GPro97/Projet_gestion_camion/images/img1.jpg

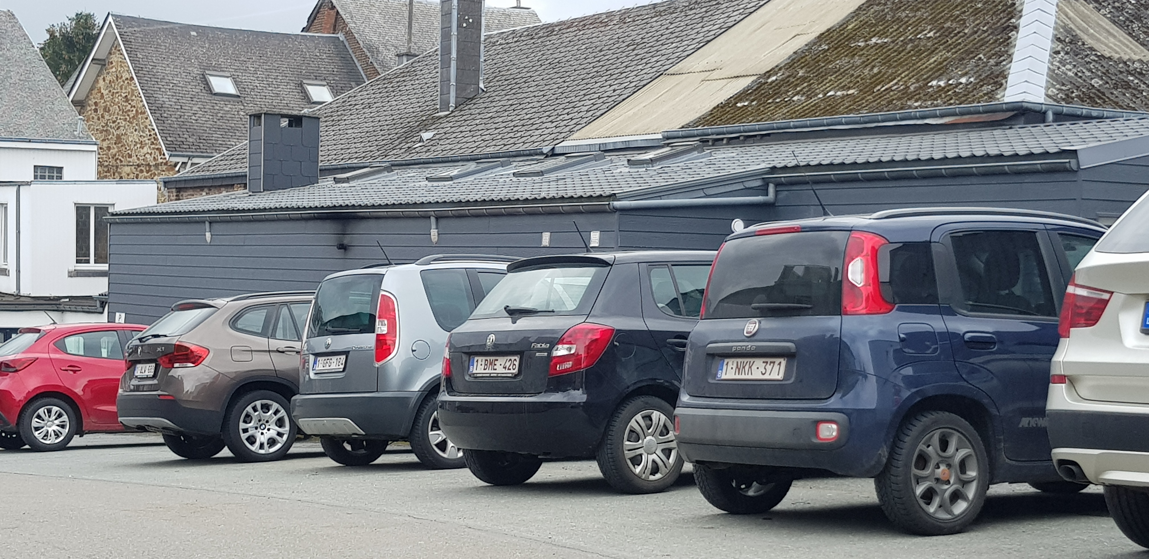
images/img1.jpg
