GPro97/Projet_gestion_camion/images/img3.jpg

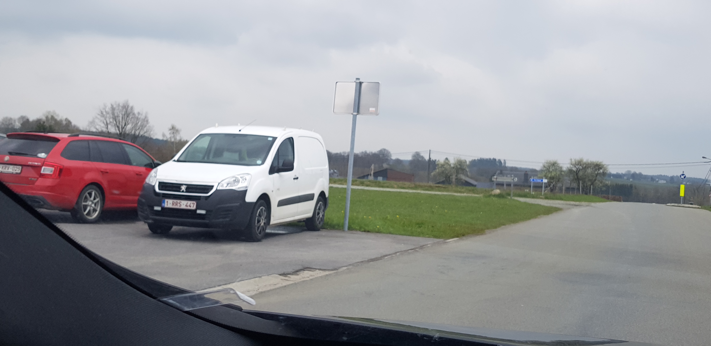
images/img3.jpg
