GPro97/Projet_gestion_camion/images/img4.jpg

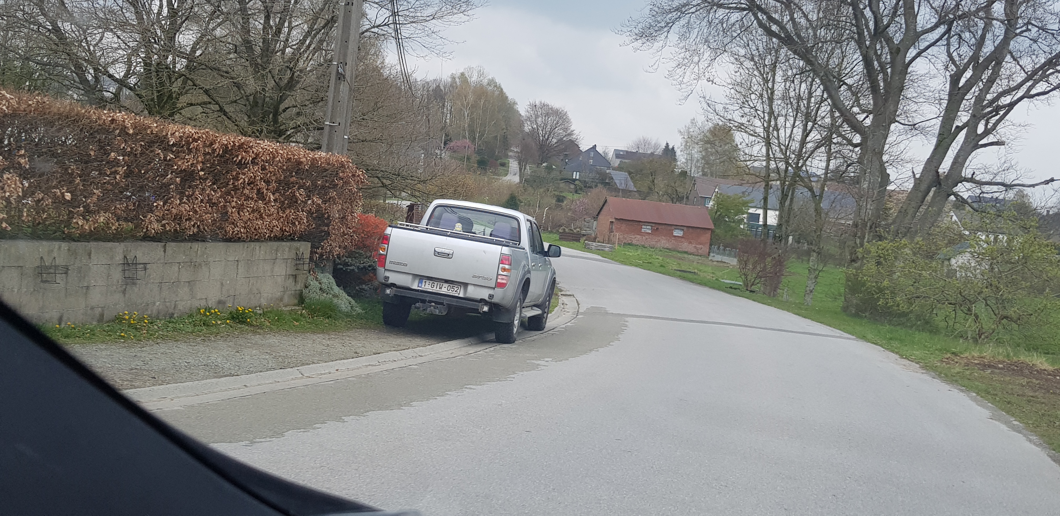
images/img4.jpg
