GPro97/Projet_gestion_camion/images/img5.jpg

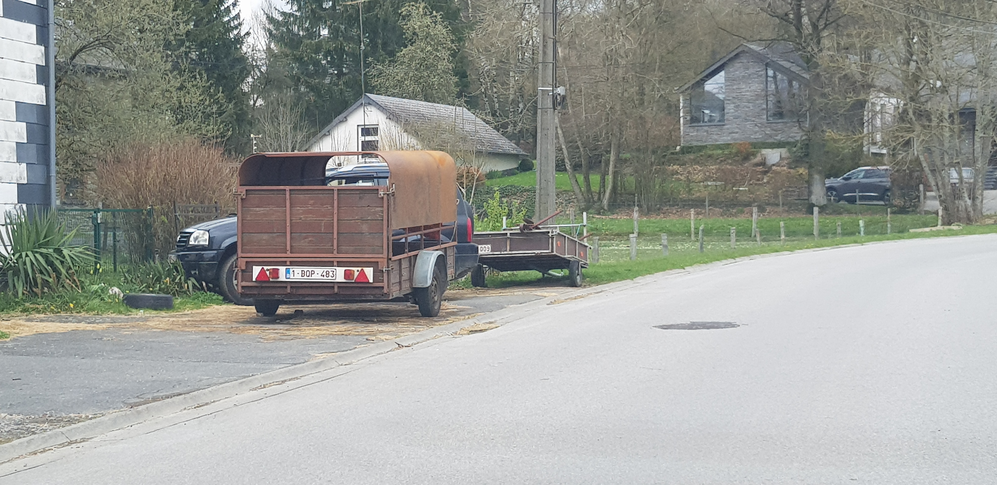
images/img5.jpg
