GPro97/Projet_gestion_camion/images/img8.jpg

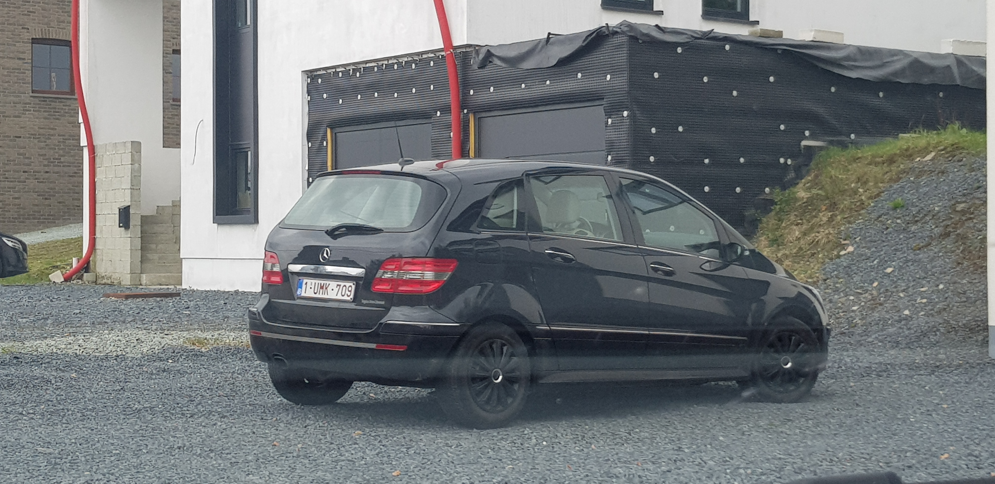
images/img8.jpg
