GPro97/Projet_gestion_camion/images/img9.jpg

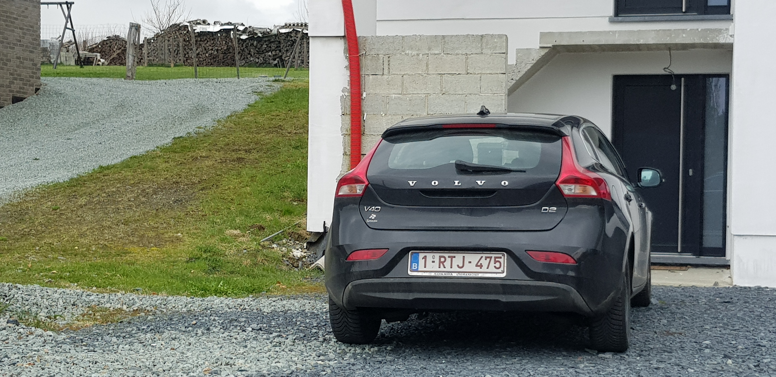
images/img9.jpg
