GPro97/Projet_gestion_camion/images/img10.jpg

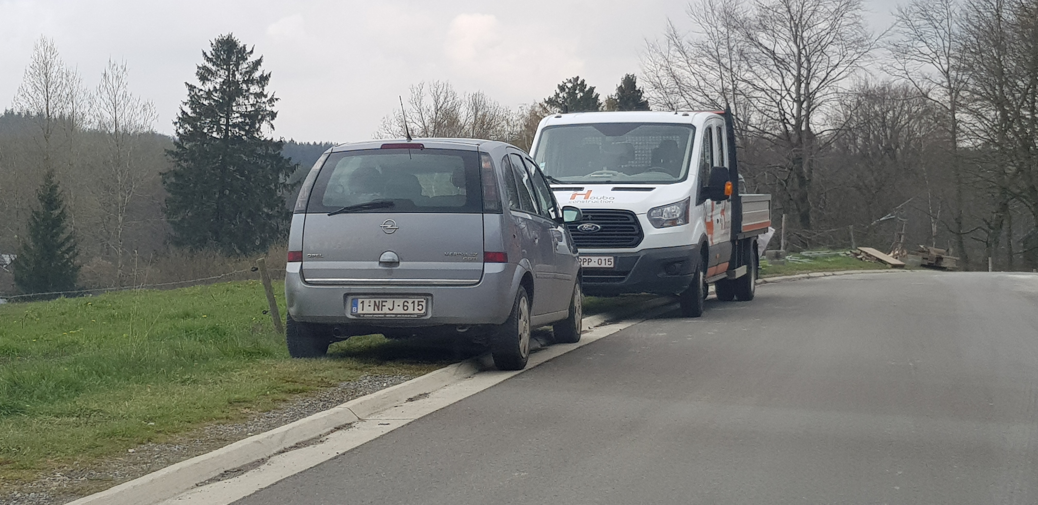
images/img10.jpg
