GPro97/Projet_gestion_camion/images/img11.jpg

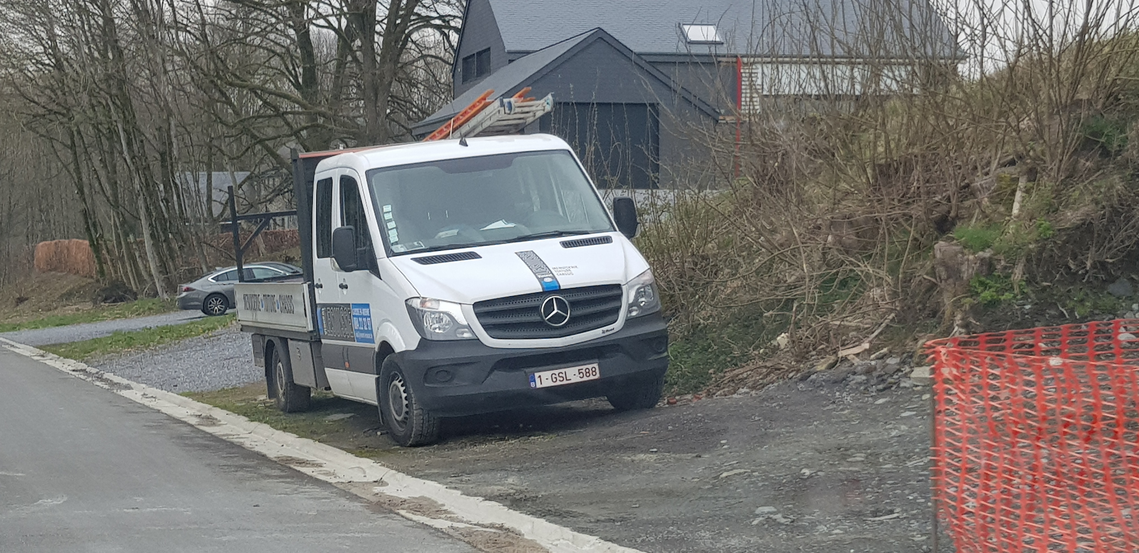
images/img11.jpg
