GPro97/Projet_gestion_camion/images/img12.jpg

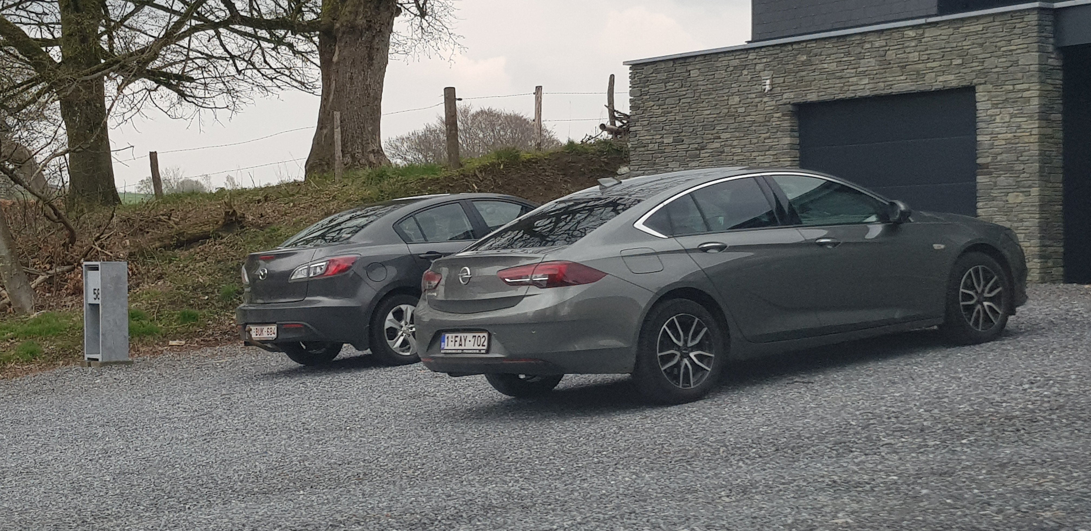
images/img12.jpg
