GPro97/Projet_gestion_camion/images/img13.jpg

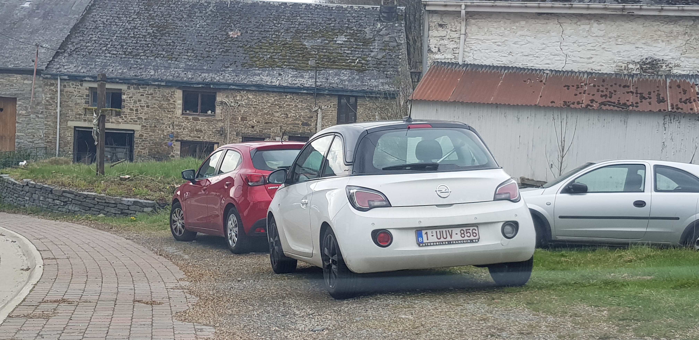
images/img13.jpg
