GPro97/Projet_gestion_camion/images/img14.jpg

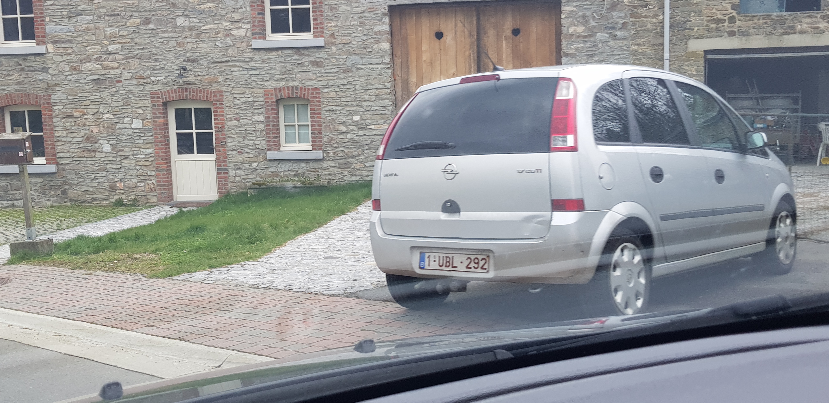
images/img14.jpg
