GPro97/Projet_gestion_camion/images/img15.jpg

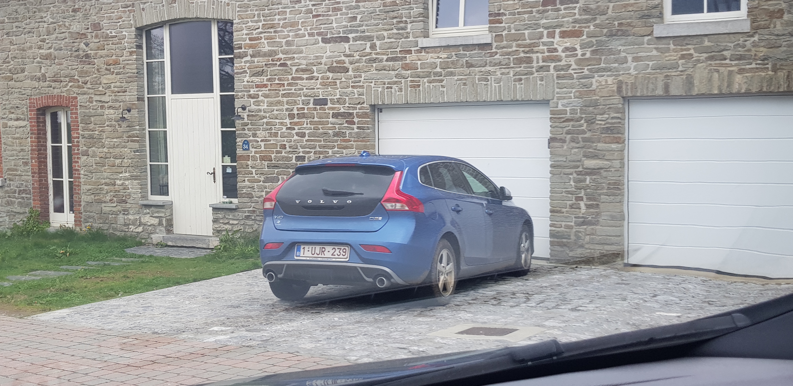
images/img15.jpg
