GPro97/Projet_gestion_camion/images/img16.jpg

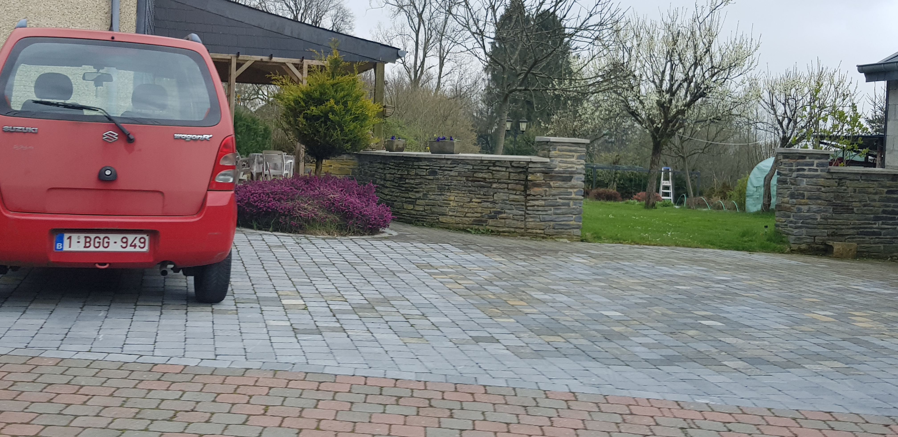
images/img16.jpg
