GPro97/Projet_gestion_camion/images/img17.jpg

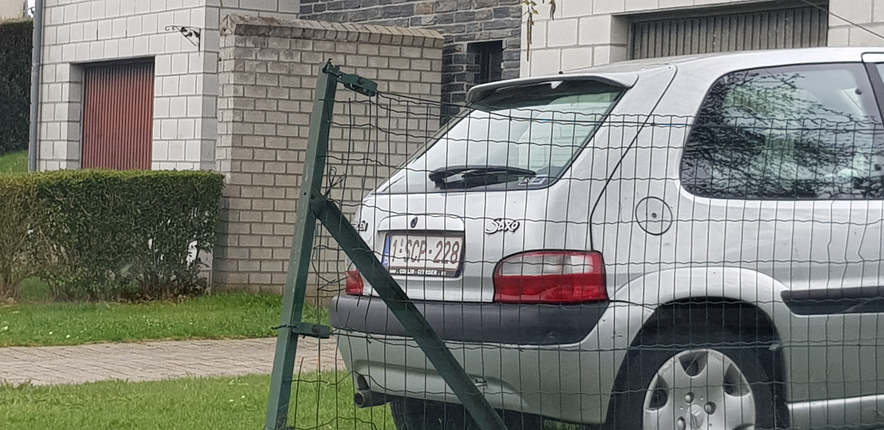
images/img17.jpg
