GPro97/Projet_gestion_camion/images/img18.jpg

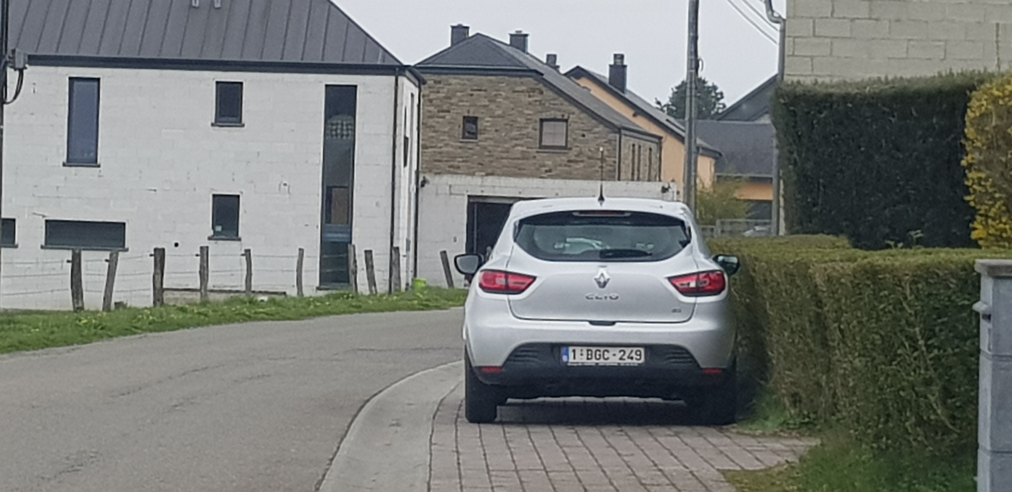
images/img18.jpg
