GPro97/Projet_gestion_camion/images/img19.jpg

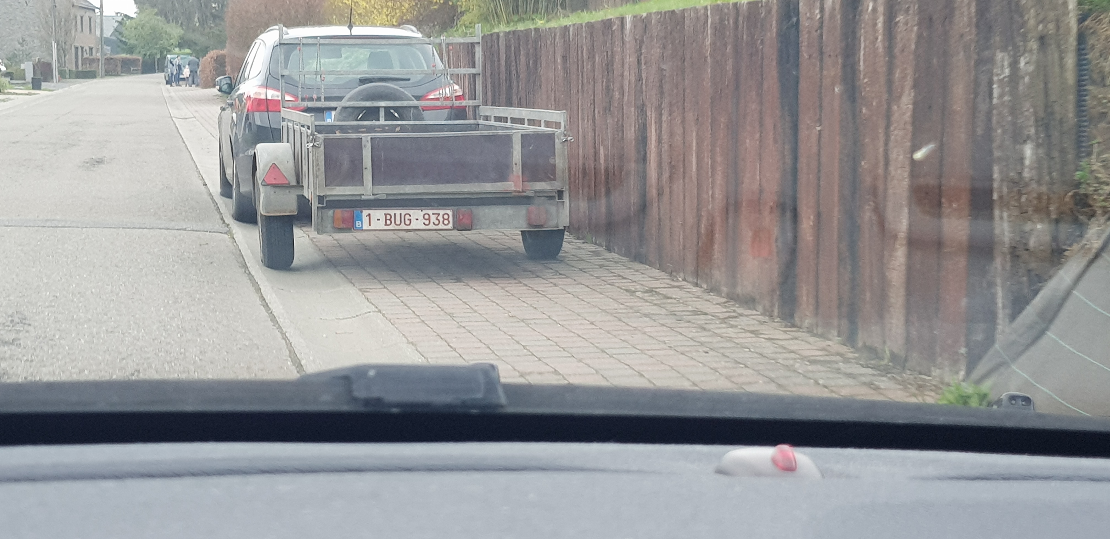
images/img19.jpg
