GPro97/Projet_gestion_camion/images/img21.jpg

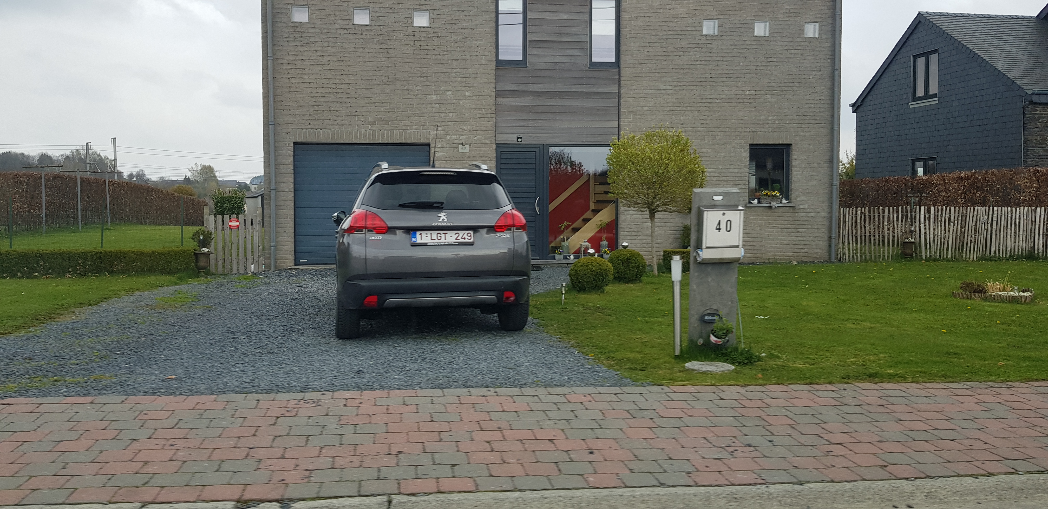
images/img21.jpg
