GPro97/Projet_gestion_camion/images/img23.jpg

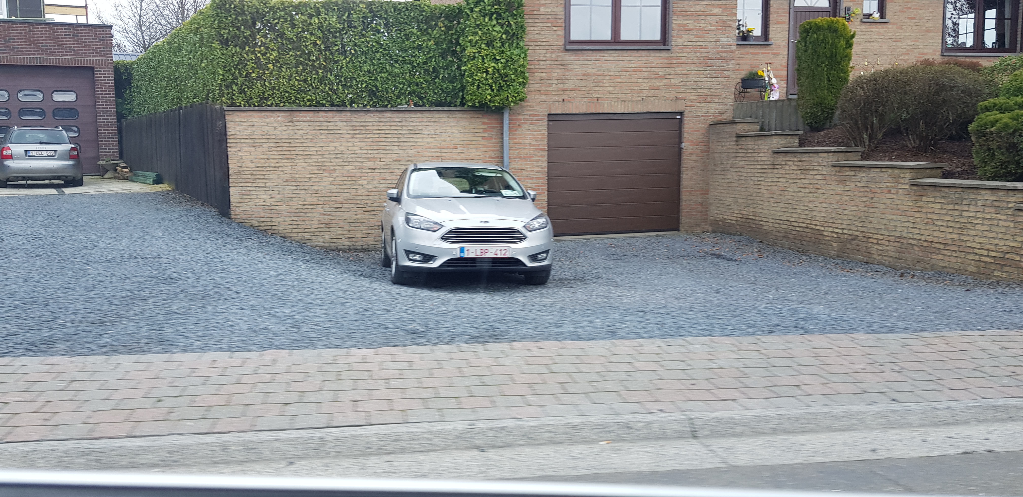
images/img23.jpg
