GPro97/Projet_gestion_camion/images/img24.jpg

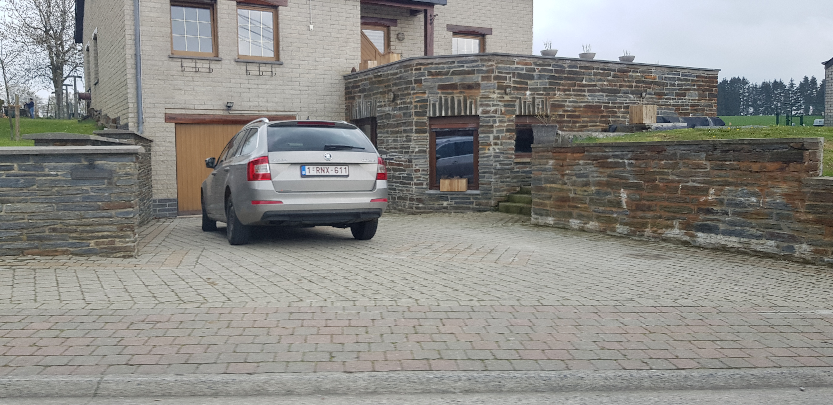
images/img24.jpg
