GPro97/Projet_gestion_camion/images/img25.jpg

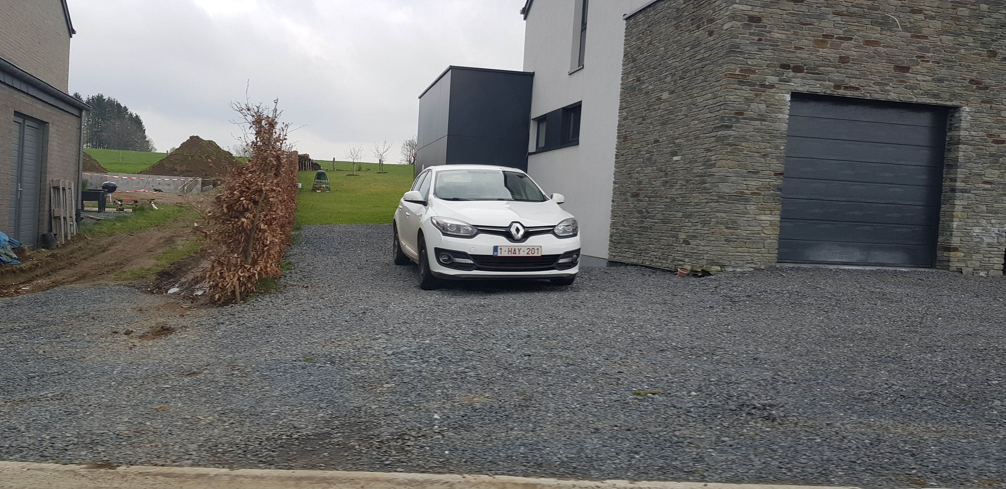
images/img25.jpg
