GPro97/Projet_gestion_camion/images/img26.jpg

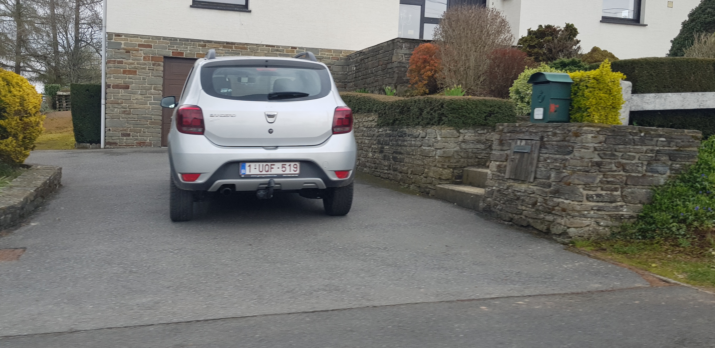
images/img26.jpg
