GPro97/Projet_gestion_camion/images/img27.jpg

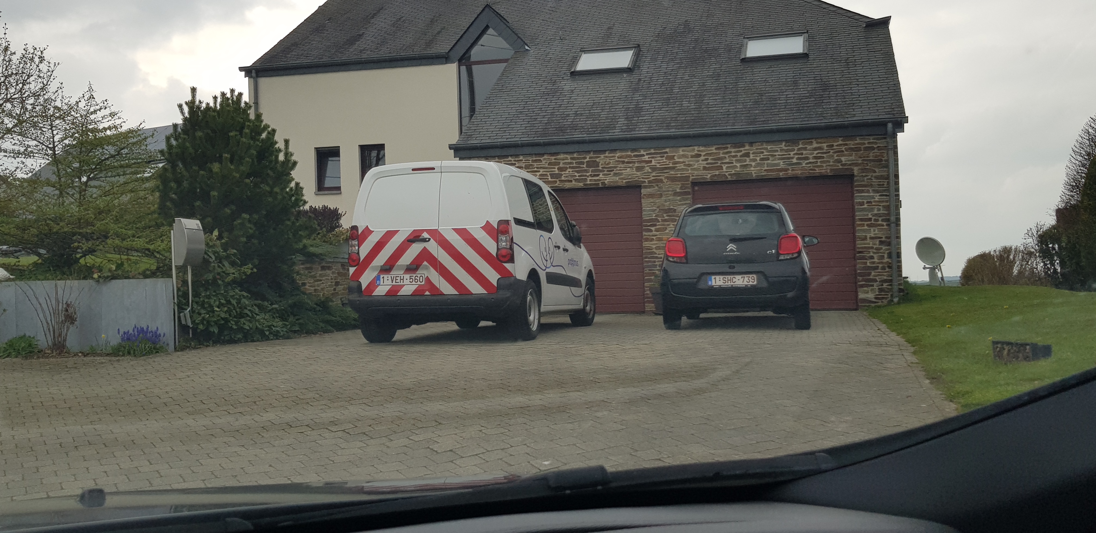
images/img27.jpg
