GPro97/Projet_gestion_camion/images/img28.jpg

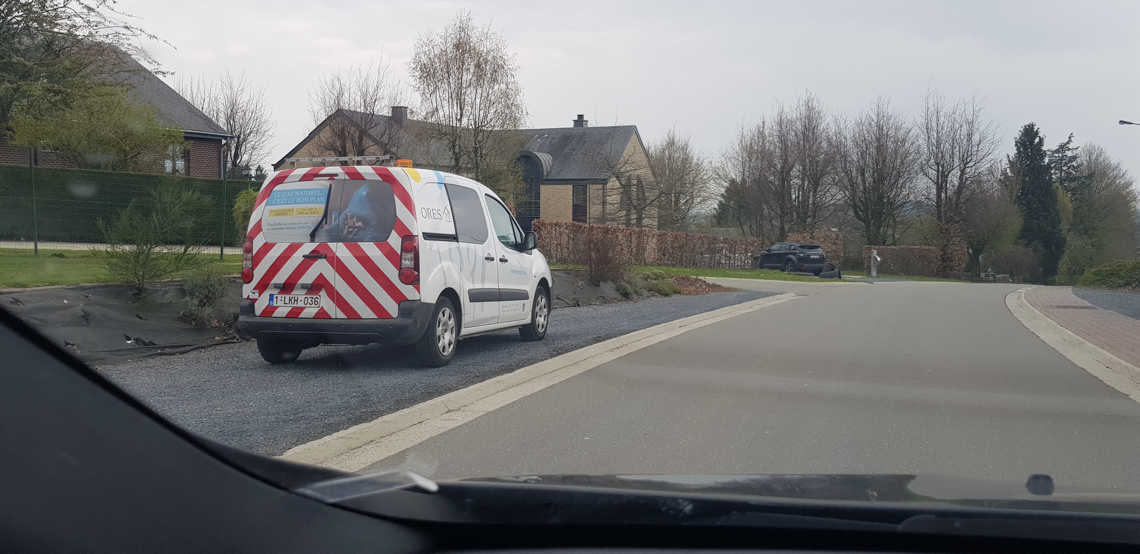
images/img28.jpg
