GPro97/Projet_gestion_camion/images/img29.jpg

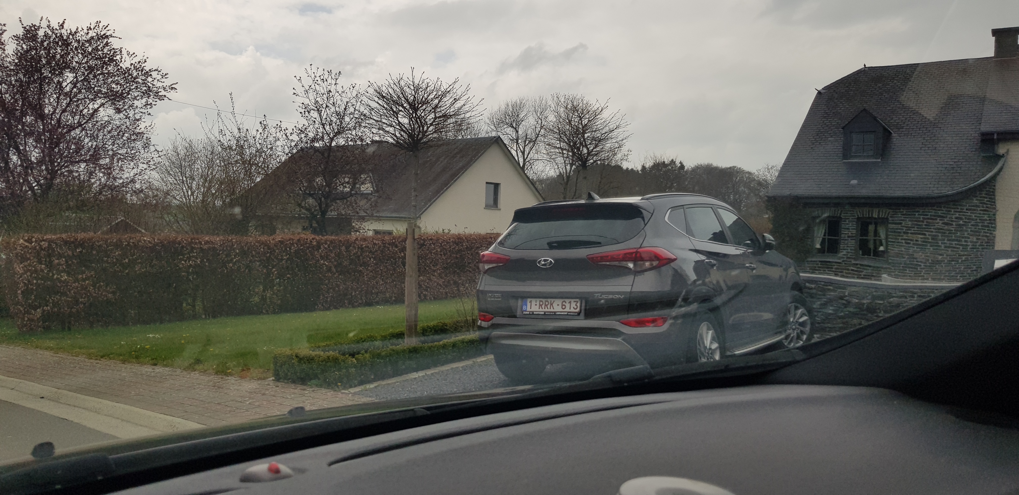
images/img29.jpg
