GPro97/Projet_gestion_camion/images/img31.jpg

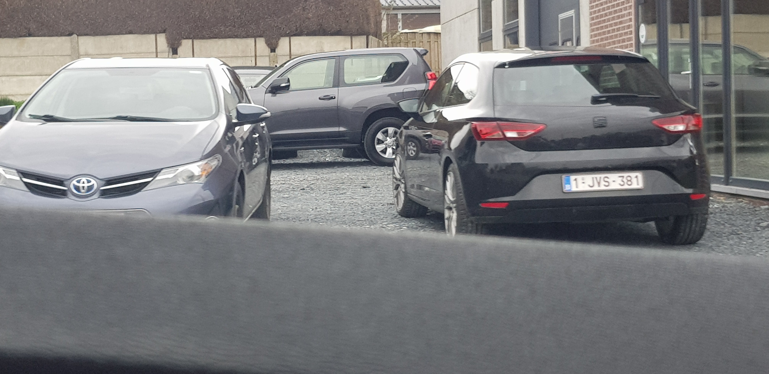
images/img31.jpg
