GPro97/Projet_gestion_camion/images/img32.jpg

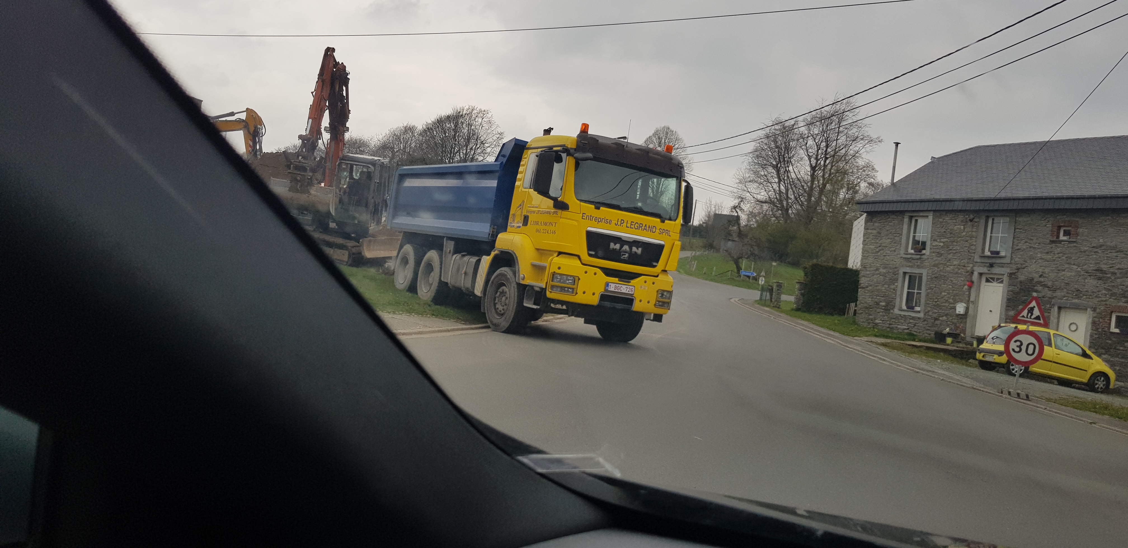
images/img32.jpg
