GPro97/Projet_gestion_camion/images/img33.jpg

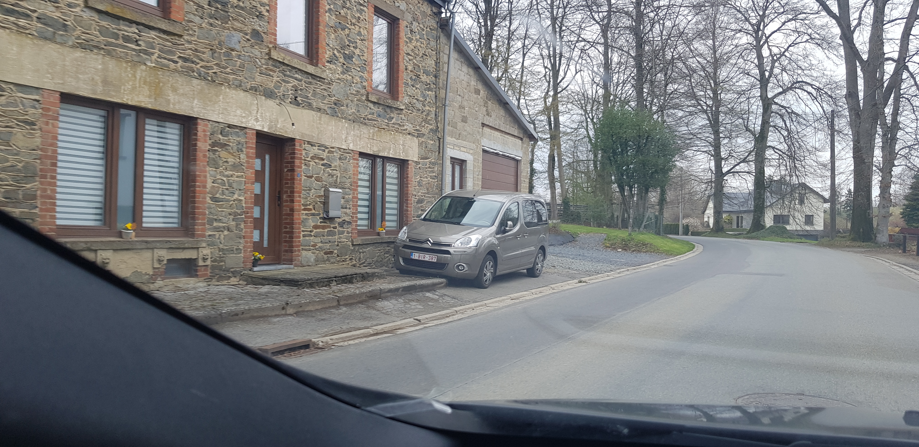
images/img33.jpg
