GPro97/Projet_gestion_camion/images/img34.jpg

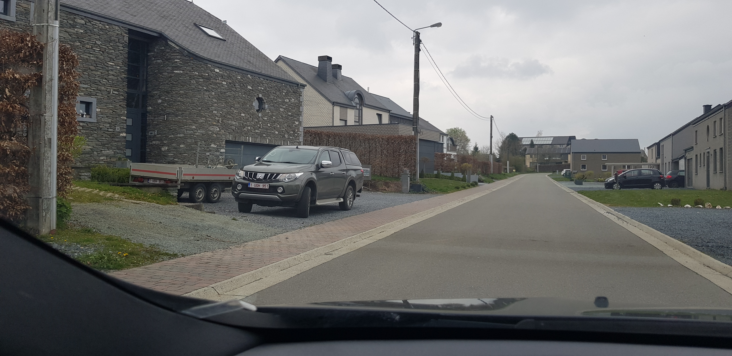
images/img34.jpg
