GPro97/Projet_gestion_camion/images/img36.jpg

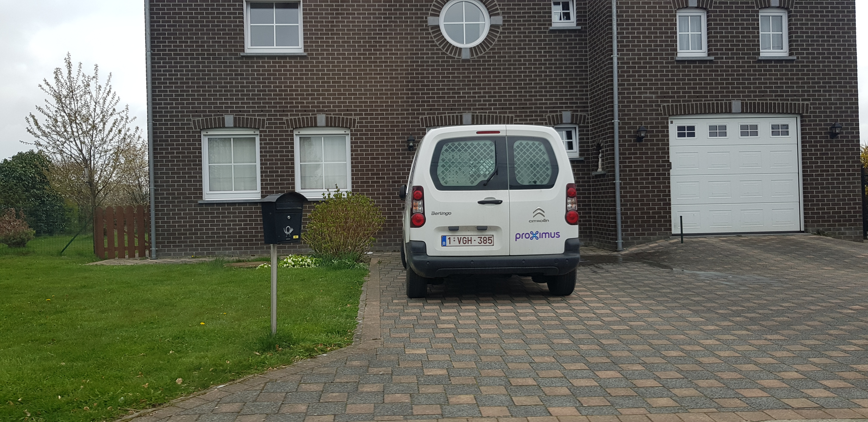
images/img36.jpg
