GPro97/Projet_gestion_camion/images/img37.jpg

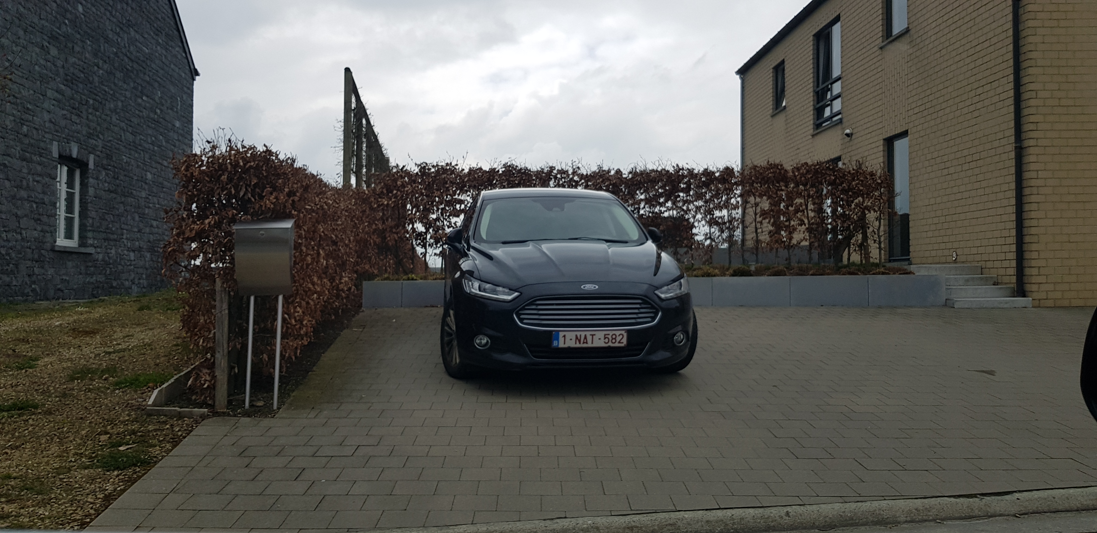
images/img37.jpg
