GPro97/Projet_gestion_camion/images/img38.jpg

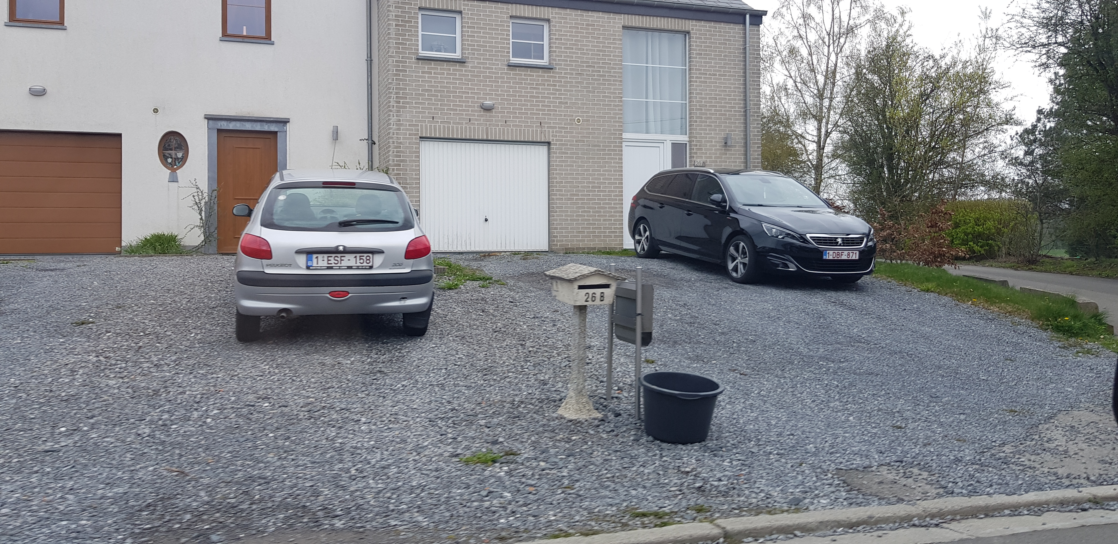
images/img38.jpg
