GPro97/Projet_gestion_camion/images/img39.jpg

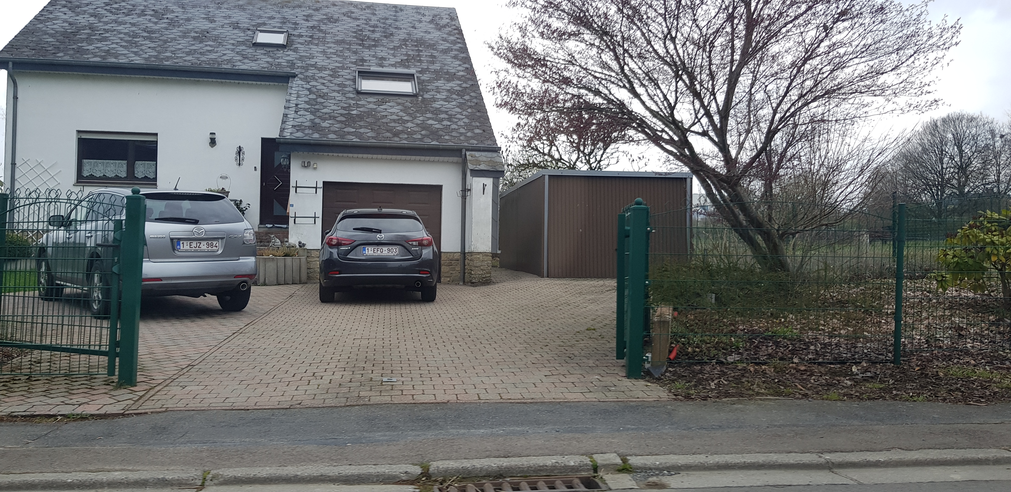
images/img39.jpg
