GPro97/Projet_gestion_camion/images/img40.jpg

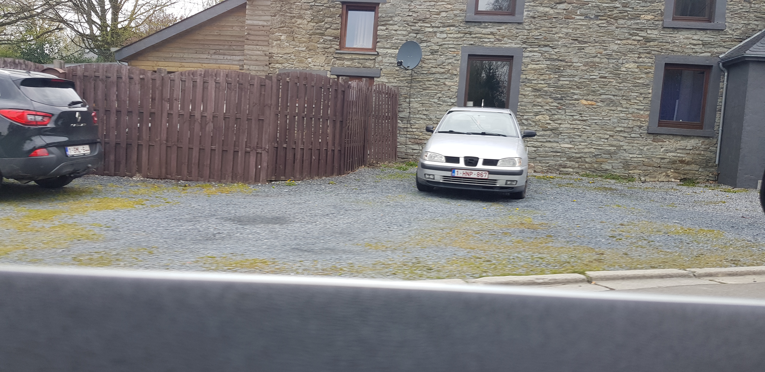
images/img40.jpg
