GPro97/Projet_gestion_camion/images/img41.jpg

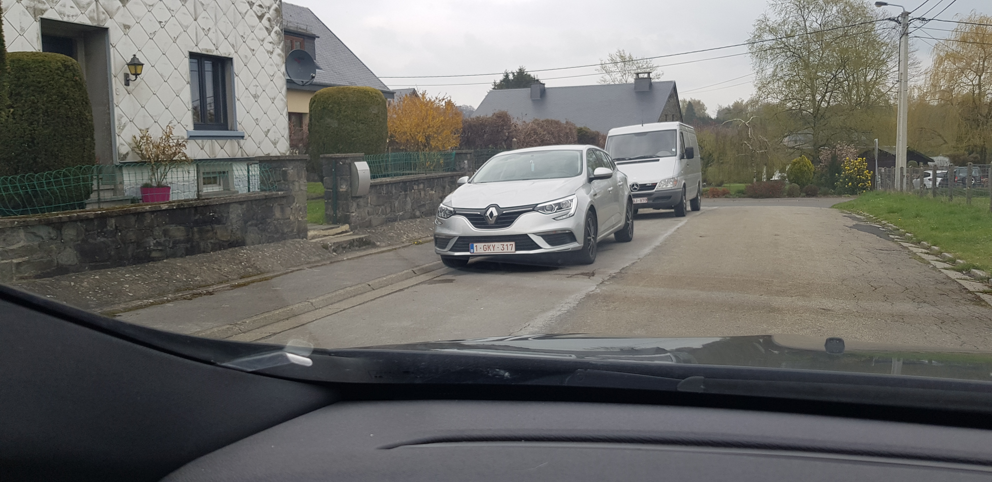
images/img41.jpg
