GPro97/Projet_gestion_camion/images/img42.jpg

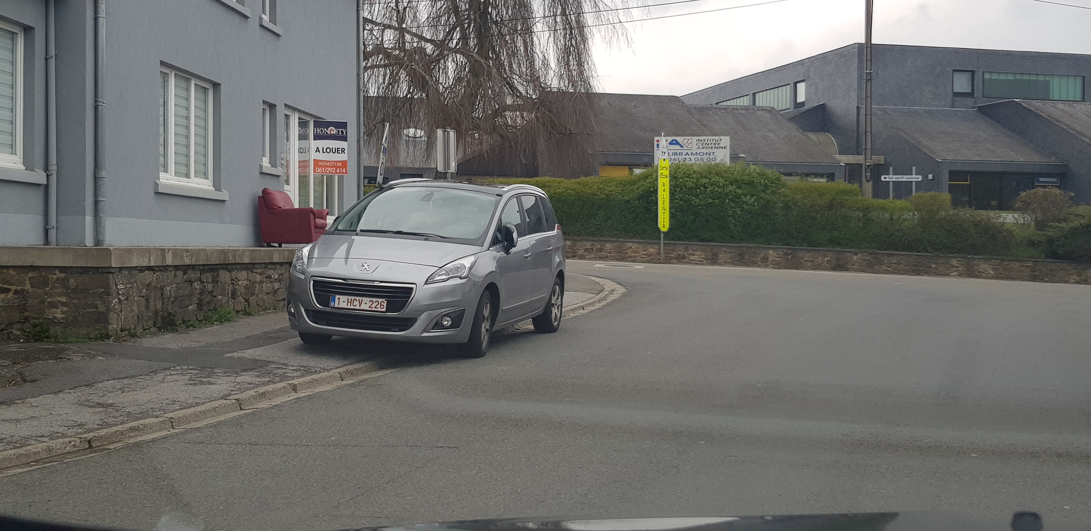
images/img42.jpg
