GPro97/Projet_gestion_camion/images/img43.jpg

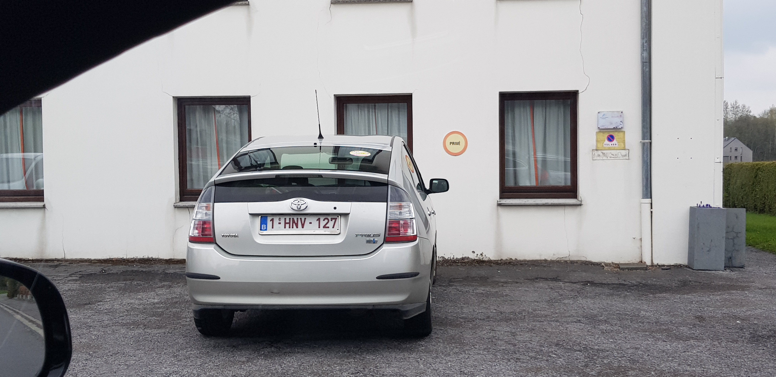
images/img43.jpg
