GPro97/Projet_gestion_camion/images/img44.jpg

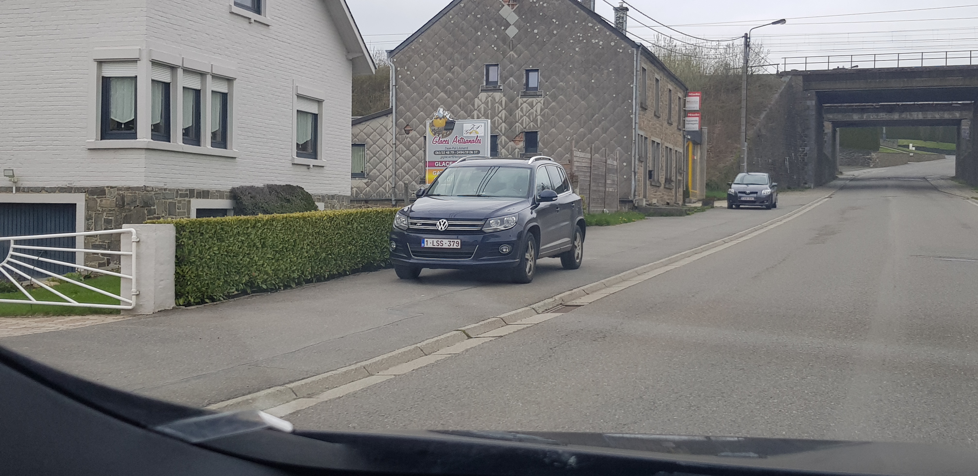
images/img44.jpg
