GPro97/Projet_gestion_camion/images/img45.jpg

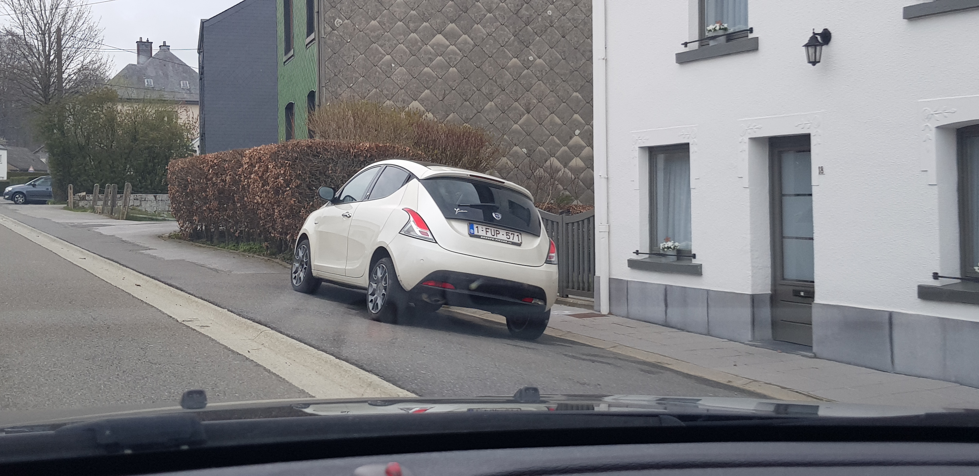
images/img45.jpg
