GPro97/Projet_gestion_camion/images/img46.jpg

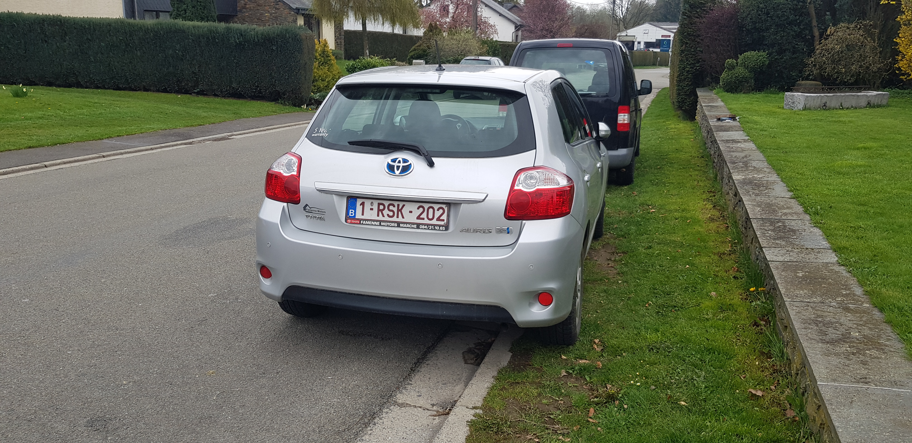
images/img46.jpg
