GPro97/Projet_gestion_camion/images/img47.jpg

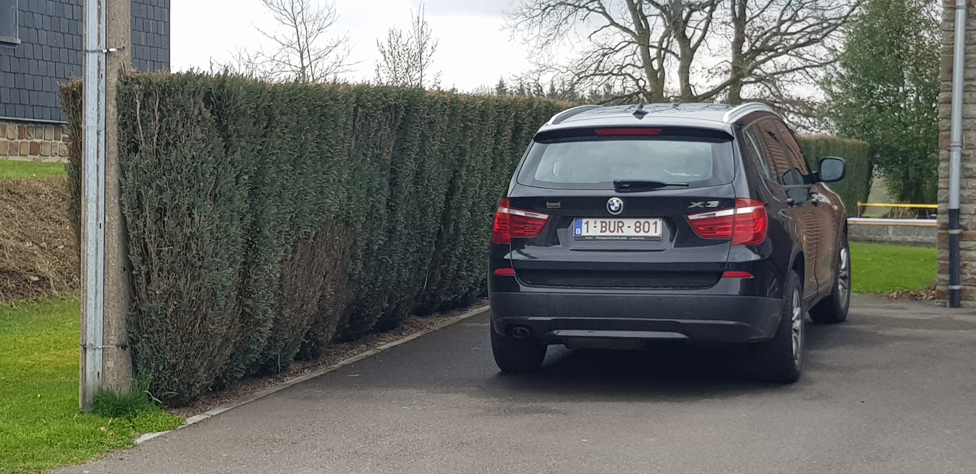
images/img47.jpg
