GPro97/Projet_gestion_camion/images/img48.jpg

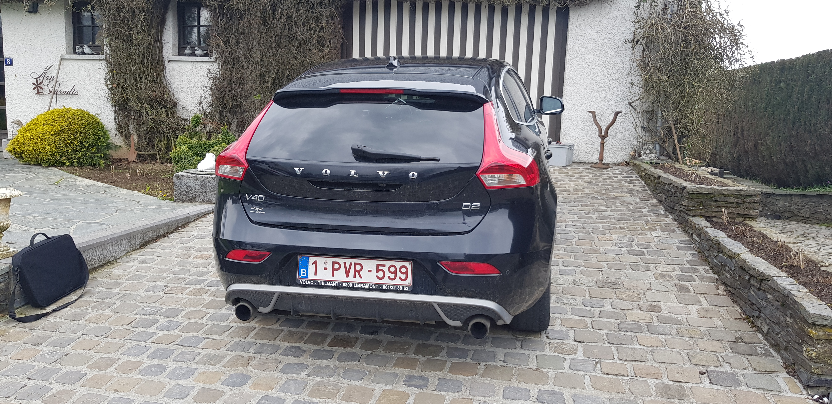
images/img48.jpg
