GPro97/Projet_gestion_camion/images/img49.jpg

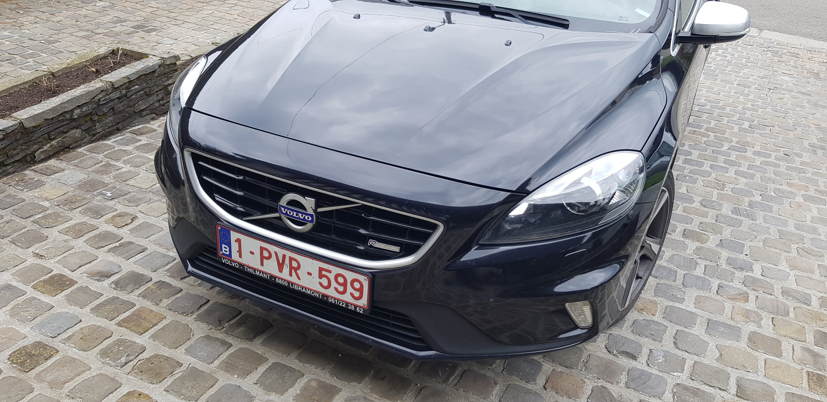
images/img49.jpg
