GPro97/Projet_gestion_camion/images/img50.jpg

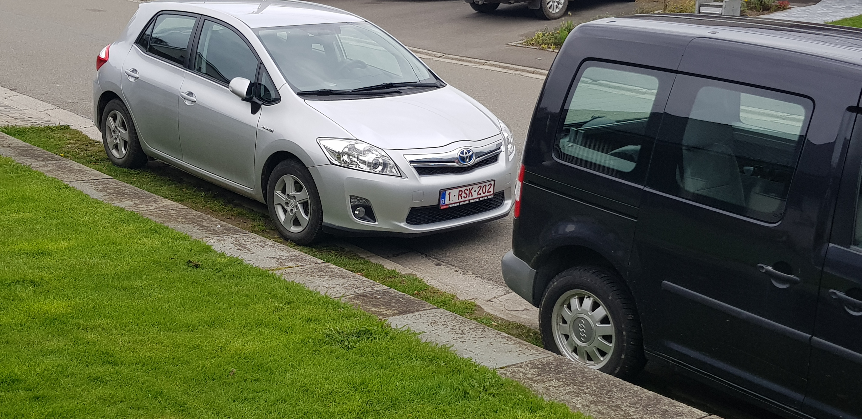
images/img50.jpg
