GPro97/Projet_gestion_camion/images/img51.jpg

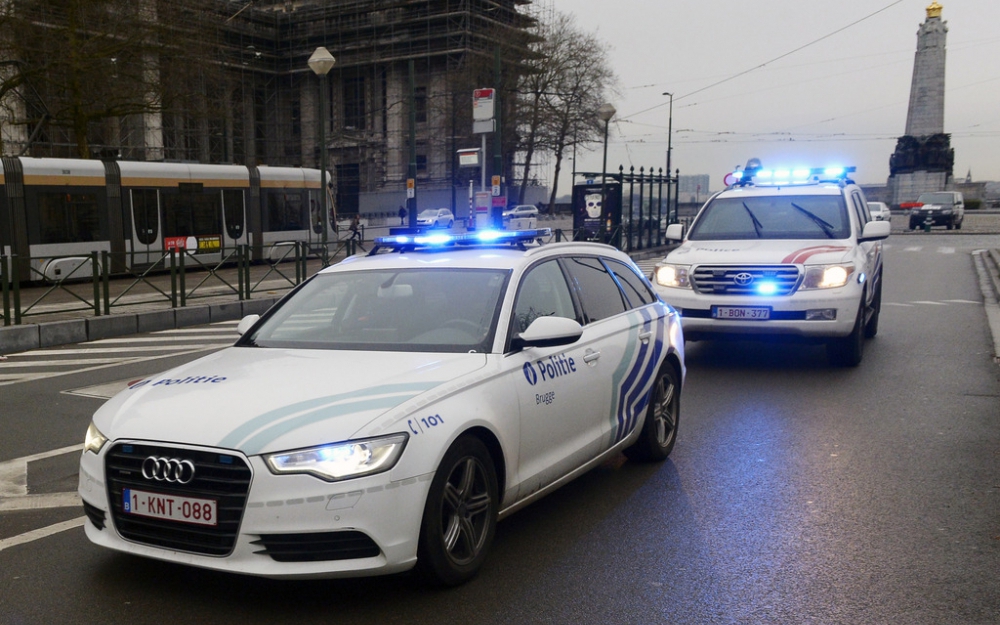
images/img51.jpg
