GPro97/Projet_gestion_camion/images/img52.jpg

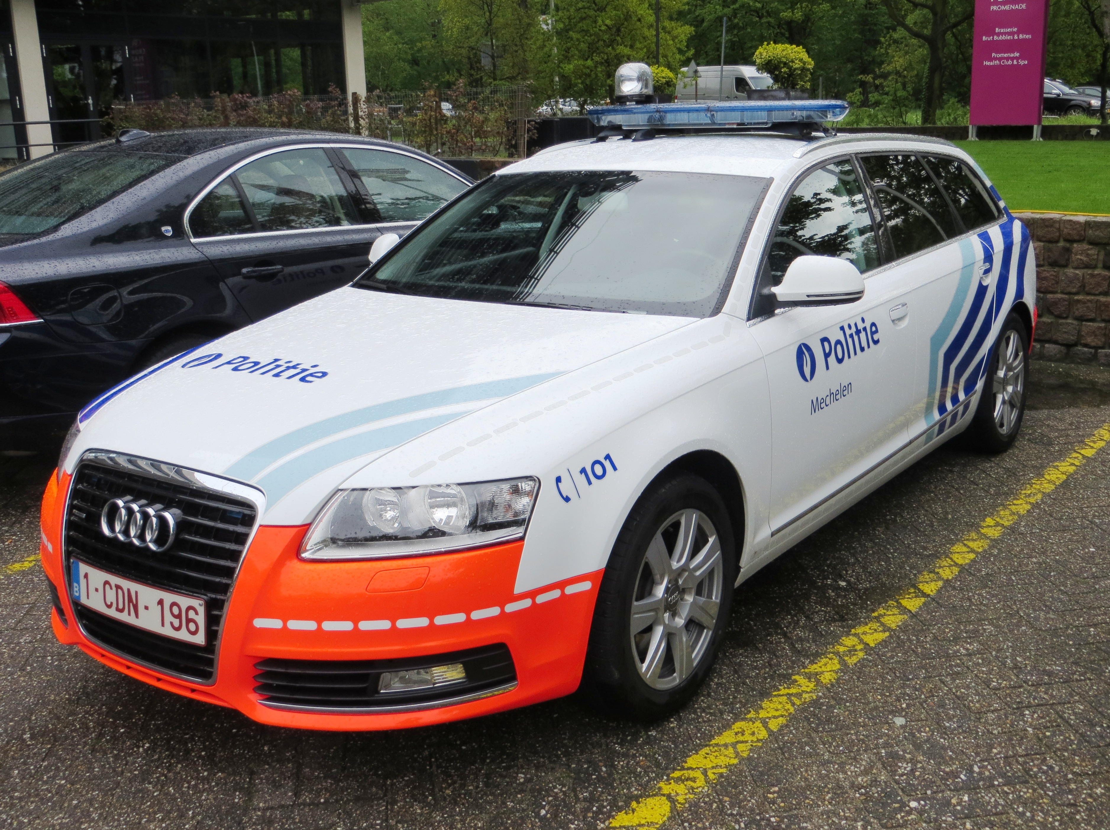
images/img52.jpg
