GPro97/Projet_gestion_camion/images/img53.jpg

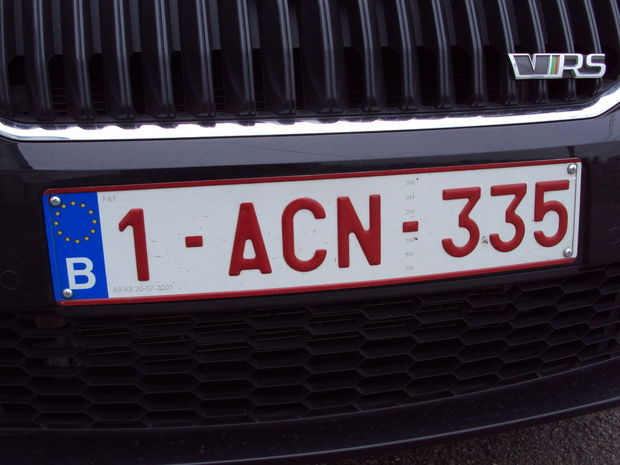
images/img53.jpg
