GPro97/Projet_gestion_camion/images/img54.jpg

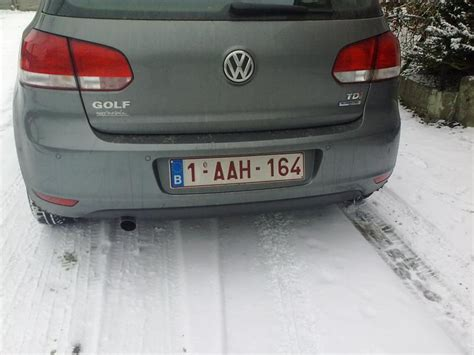
images/img54.jpg
