GPro97/Projet_gestion_camion/images/img56.jpg

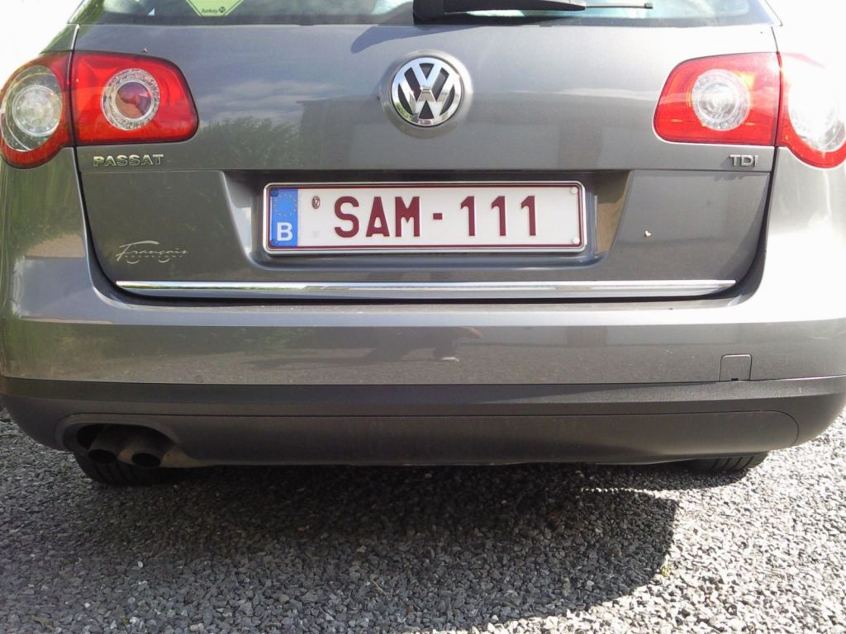
images/img56.jpg
