GPro97/Projet_gestion_camion/images/img59.jpg

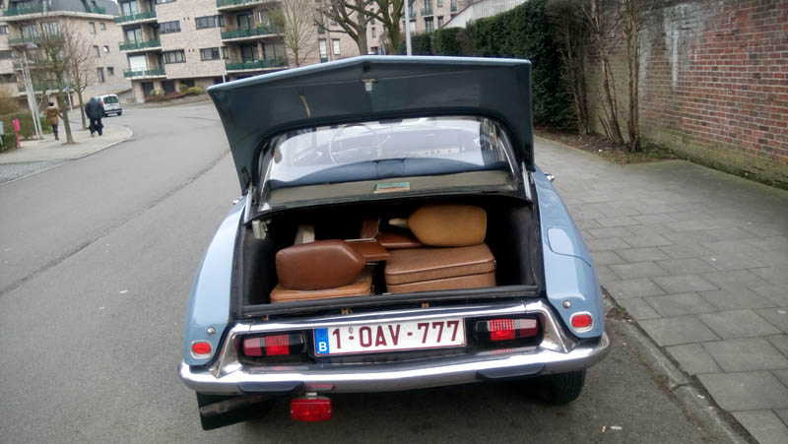
images/img59.jpg
