GPro97/Projet_gestion_camion/images/img60.jpg

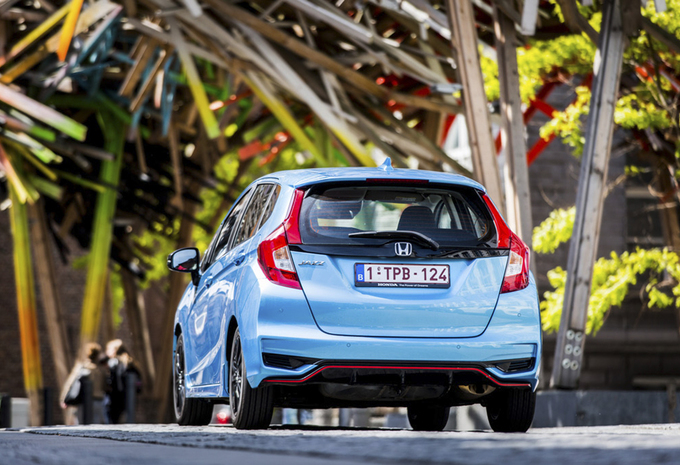
images/img60.jpg
