GPro97/Projet_gestion_camion/images/img61.jpg

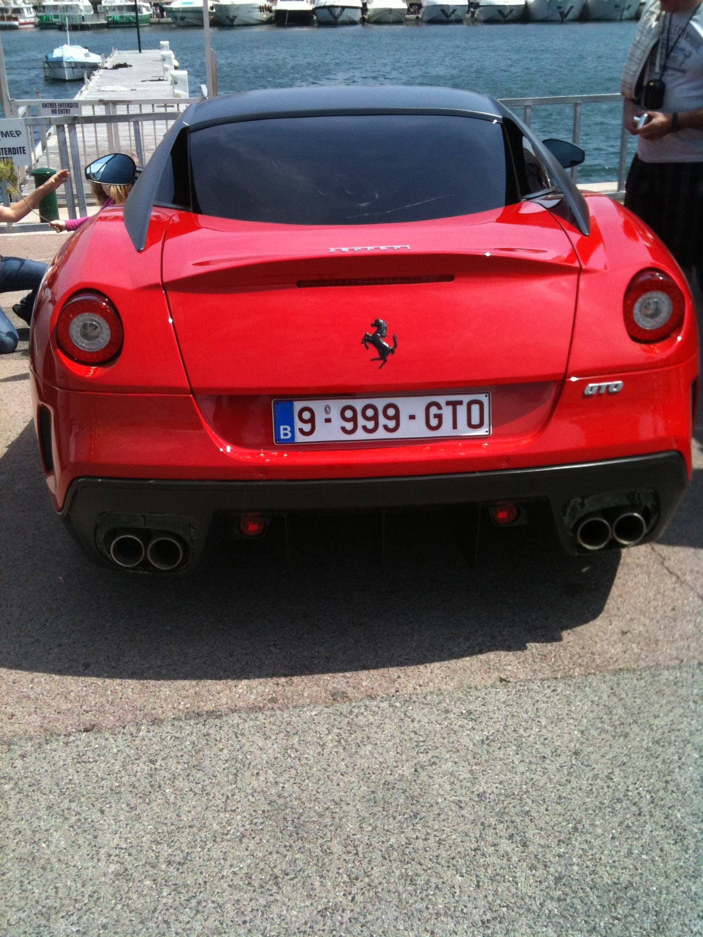
images/img61.jpg
