GPro97/Projet_gestion_camion/images/img62.jpg

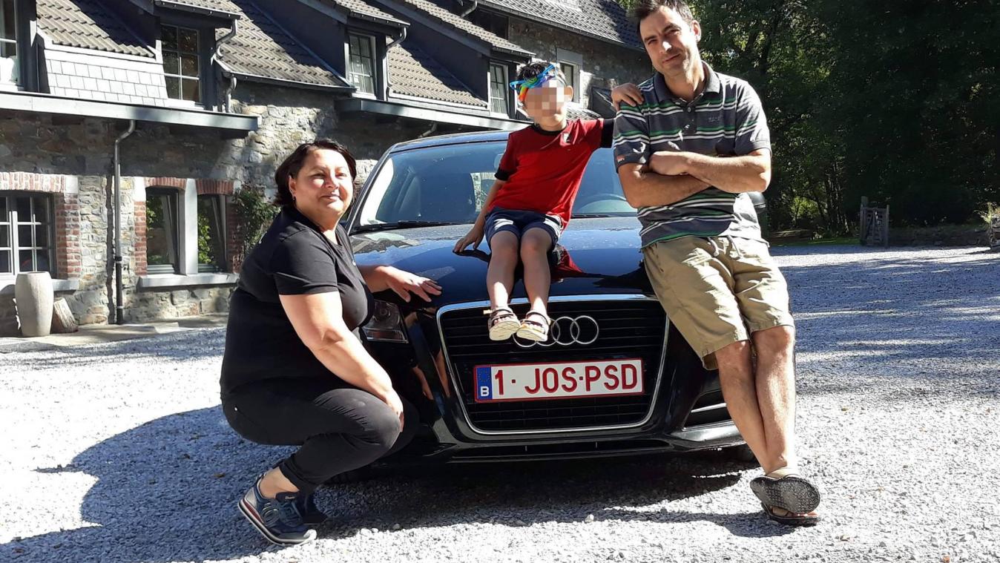
images/img62.jpg
