GPro97/Projet_gestion_camion/images/img64.jpg

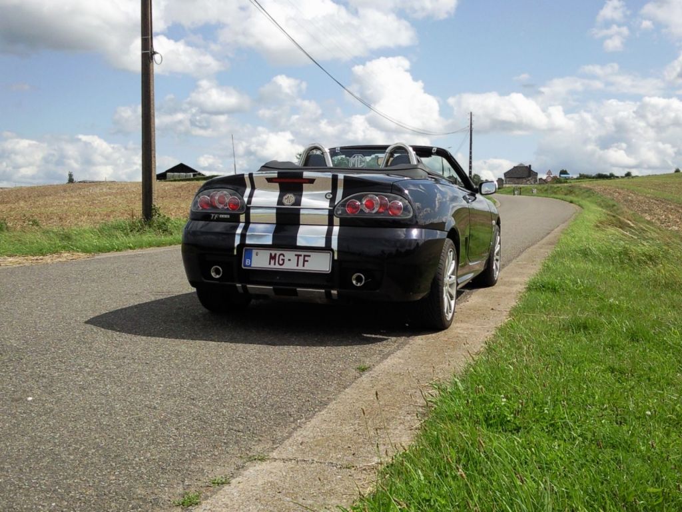
images/img64.jpg
