GPro97/Projet_gestion_camion/images/img67.jpg

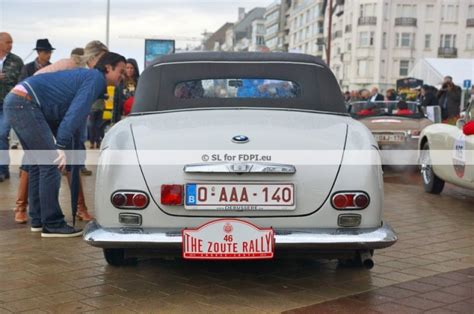
images/img67.jpg
