GPro97/Projet_gestion_camion/Schéma de câblage de l'arduino - 03_04_19.PNG

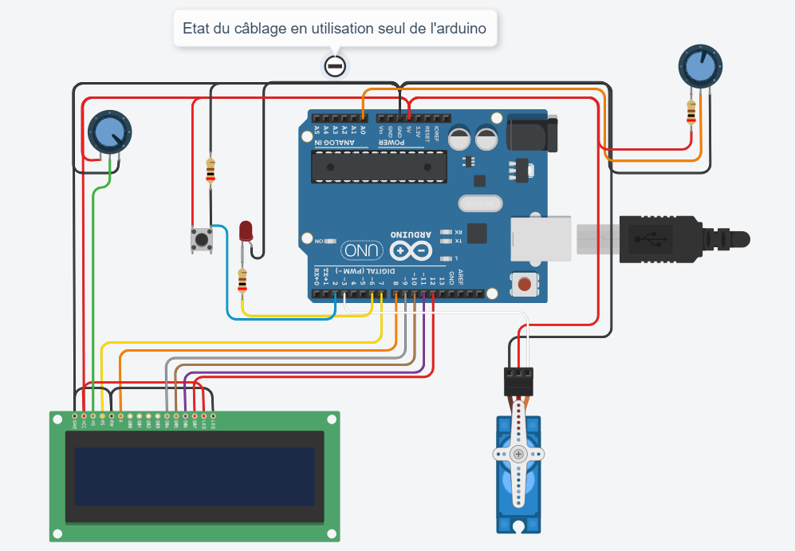
Schéma de câblage de l'arduino - 03_04_19.PNG
